henrebotha/pangolin/parts/2d/24-30/24-30-TopPanel_Snap-in.dxf

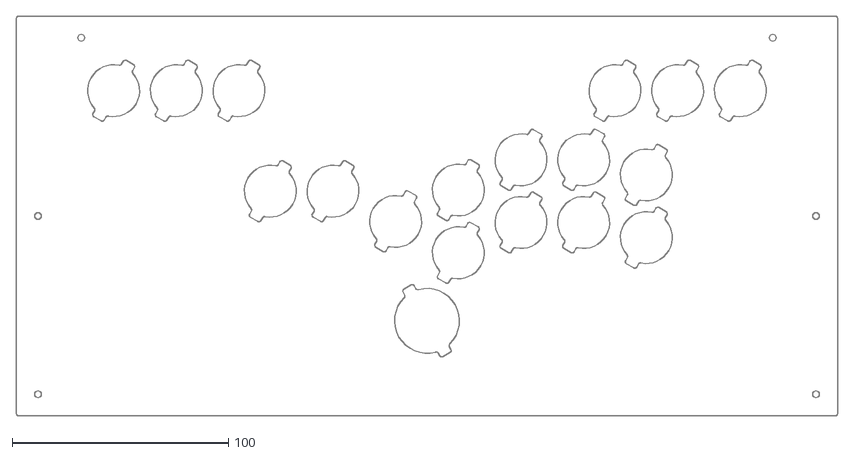
[picture p17: CAD file, 2023-01-11]
parts/2d/24-30/24-30-TopPanel_Snap-in.dxf
380.0 x 185.0
