henrebotha/pangolin/parts/2d/SwitchPlate.dxf

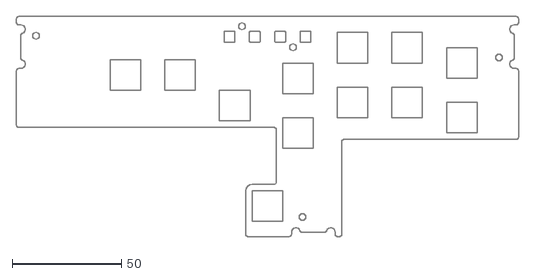
[picture p18: CAD file, 2022-08-01]
parts/2d/SwitchPlate.dxf
230.0 x 100.8
