henrebotha/pangolin/parts/2d/24-30/24-30-JackPanel.dxf

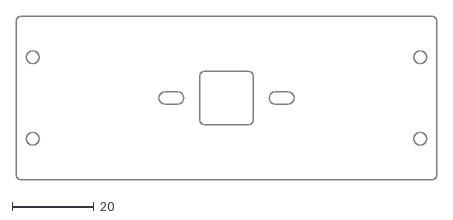
[picture p19: CAD file, 2023-01-11]
parts/2d/24-30/24-30-JackPanel.dxf
103.0 x 40.0
